ubogdan/esp8266-sprinkler-controller/photos/03 Soldering ESP8266 In Progress.jpg

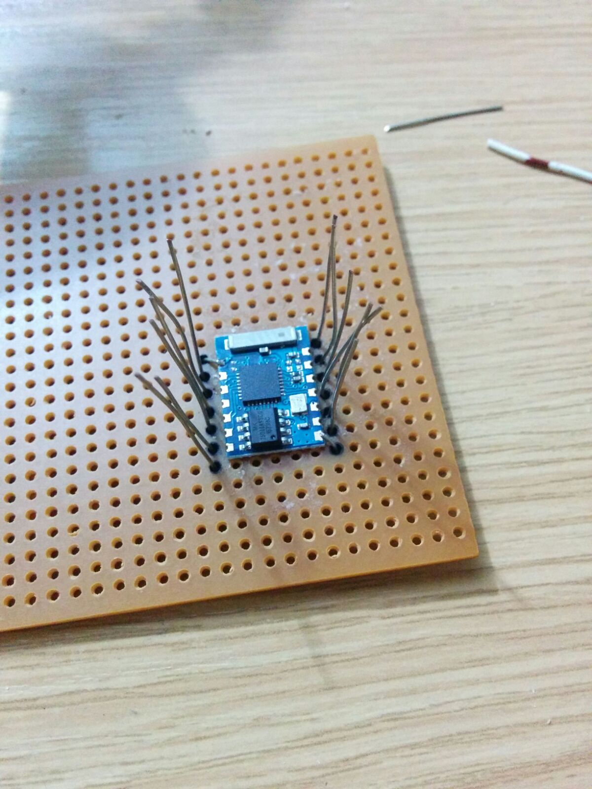
photos/03 Soldering ESP8266 In Progress.jpg
