ubogdan/esp8266-sprinkler-controller/photos/04 Soldering ESP8266 Complete.jpg

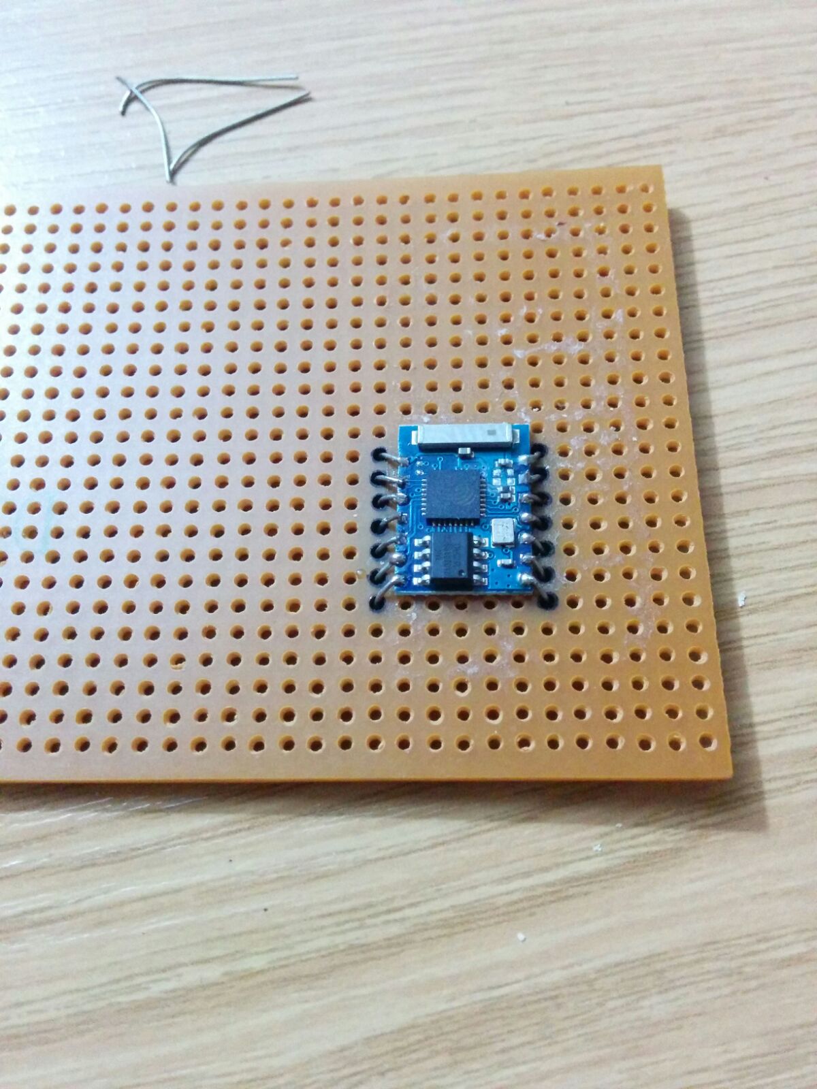
photos/04 Soldering ESP8266 Complete.jpg
