ubogdan/esp8266-sprinkler-controller/photos/08 Printing Case.jpg

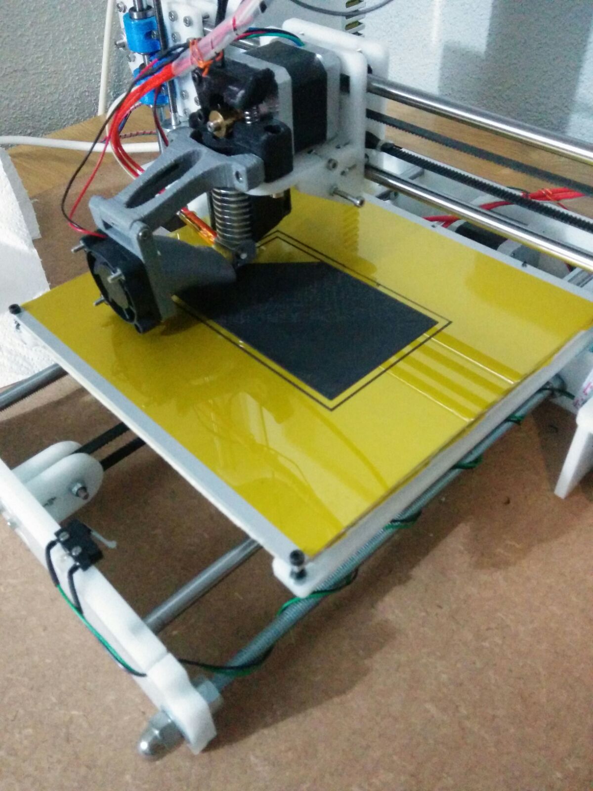
photos/08 Printing Case.jpg
