ubogdan/esp8266-sprinkler-controller/photos/09 Assembled Case.jpg

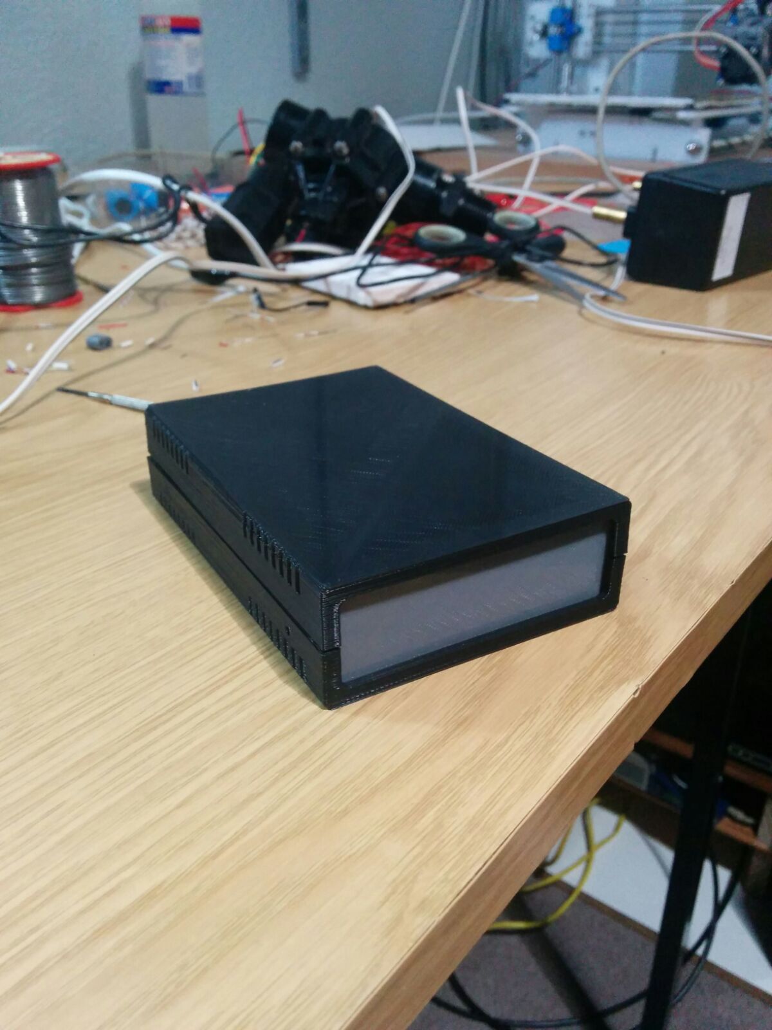
photos/09 Assembled Case.jpg
