ubogdan/esp8266-sprinkler-controller/photos/06 Testing Completed Circuit.jpg

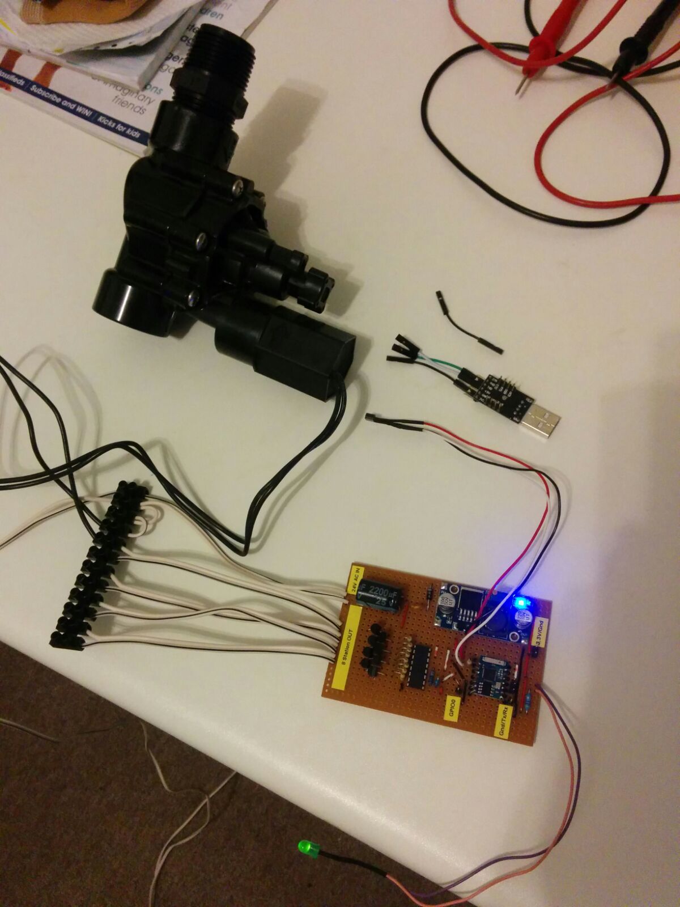
photos/06 Testing Completed Circuit.jpg
